juarendra/SlimeVR-BMI160/DOC/slimeVR_2.png

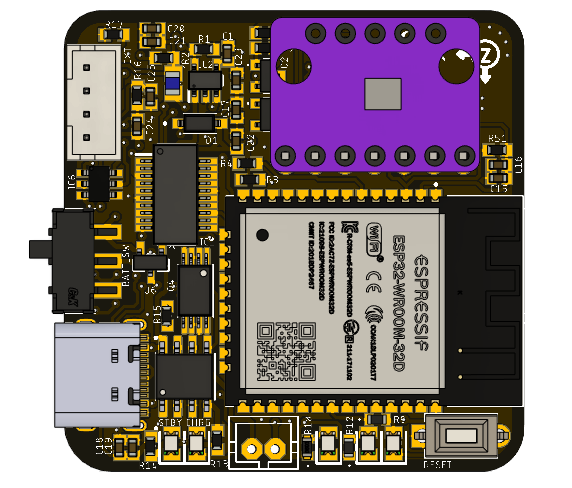
DOC/slimeVR_2.png
