juarendra/SlimeVR-BMI160/DOC/slimeVR_3.png

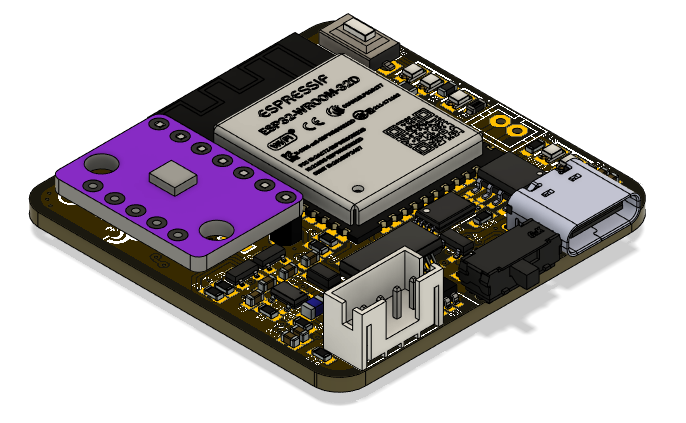
DOC/slimeVR_3.png
