juarendra/SlimeVR-BMI160/DOC/slimeVR_4.png

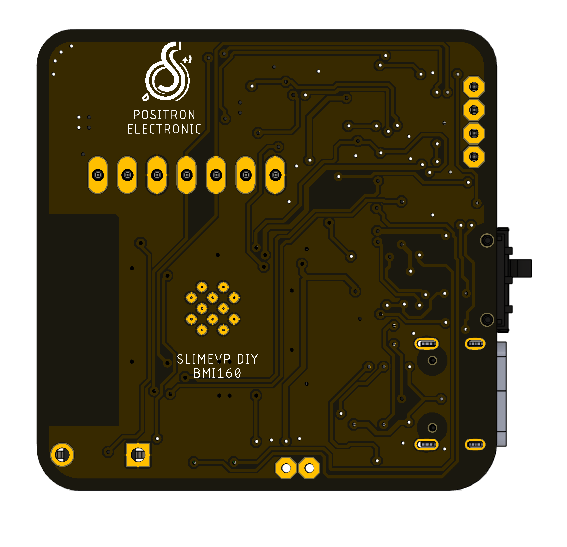
DOC/slimeVR_4.png
