juarendra/SlimeVR-BMI160/DOC/slimeVR_case_2.png

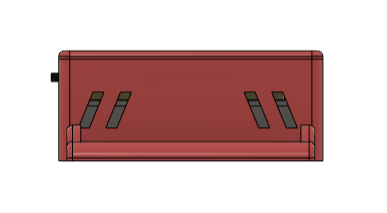
DOC/slimeVR_case_2.png
