juarendra/SlimeVR-BMI160/DOC/slimeVR_case_6.png

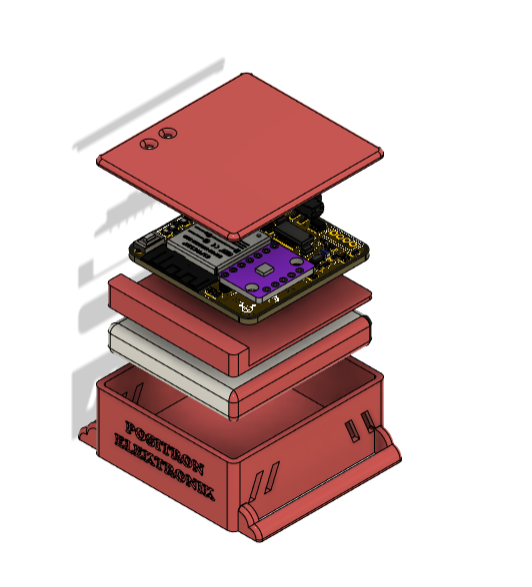
DOC/slimeVR_case_6.png
