juarendra/SlimeVR-BMI160/DOC/slimeVR_real_2.jpeg

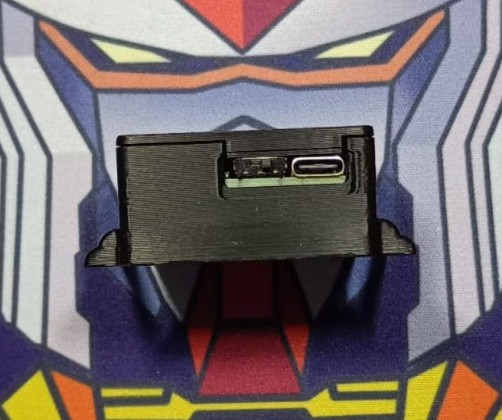
DOC/slimeVR_real_2.jpeg
