juarendra/SlimeVR-BMI160/site/assets/positron.jpg

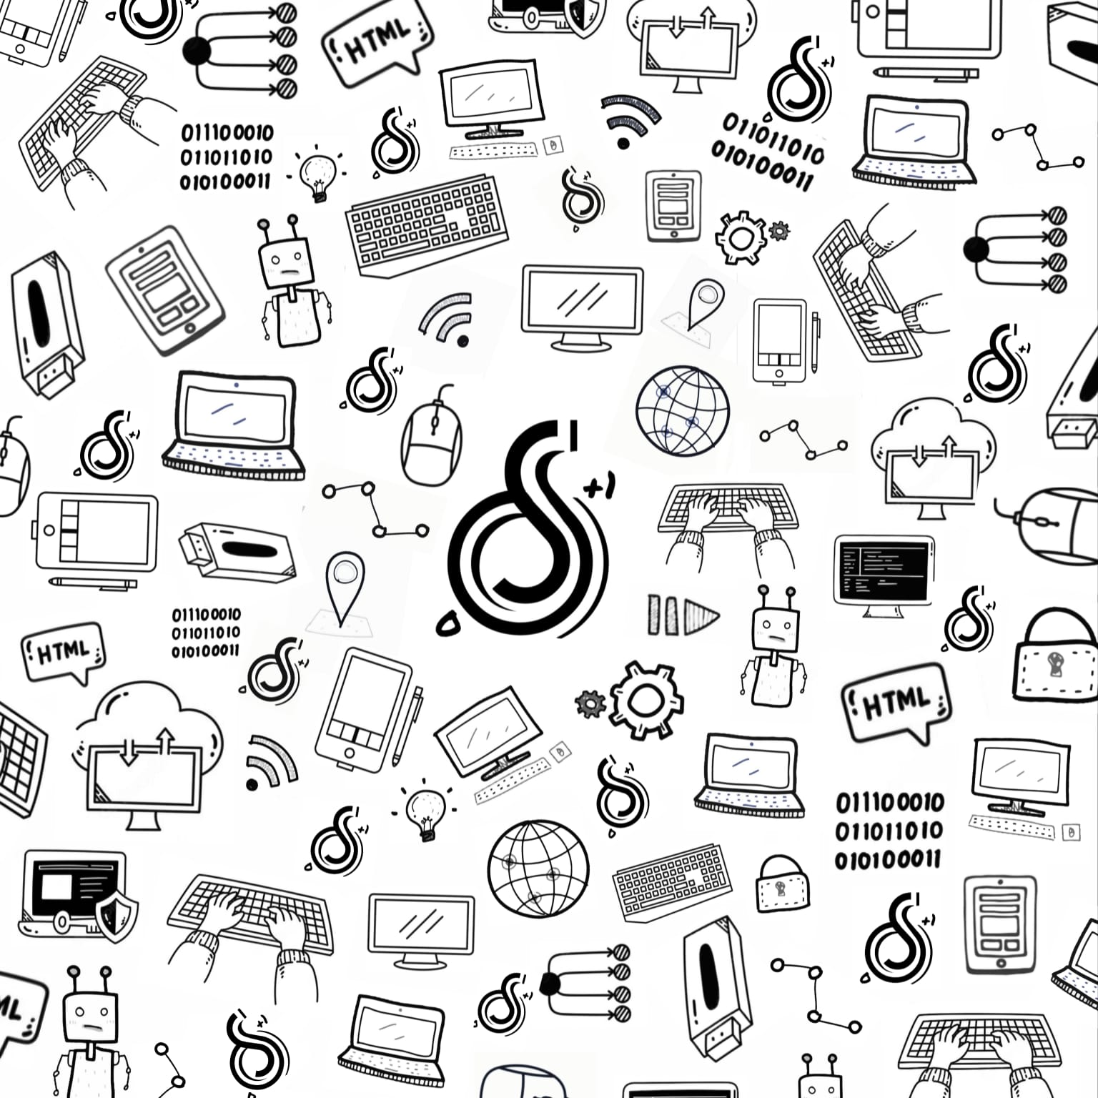
site/assets/positron.jpg
