juarendra/SlimeVR-BMI160/FIRMWARE/SlimeVR-Tracker-ESP/src/batterymonitor.cpp

/*
	SlimeVR Code is placed under the MIT license
	Copyright (c) 2021 Eiren Rain & SlimeVR contributors

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
	THE SOFTWARE IS PROVIDED "AS IS", WITHOUT WARRANTY OF ANY KIND, EXPRESS OR
	IMPLIED, INCLUDING BUT NOT LIMITED TO THE WARRANTIES OF MERCHANTABILITY,
	FITNESS FOR A PARTICULAR PURPOSE AND NONINFRINGEMENT. IN NO EVENT SHALL THE
	AUTHORS OR COPYRIGHT HOLDERS BE LIABLE FOR ANY CLAIM, DAMAGES OR OTHER
	LIABILITY, WHETHER IN AN ACTION OF CONTRACT, TORT OR OTHERWISE, ARISING FROM,
	OUT OF OR IN CONNECTION WITH THE SOFTWARE OR THE USE OR OTHER DEALINGS IN
	THE SOFTWARE.
*/
#include "batterymonitor.h"

#include "GlobalVars.h"

#if ESP8266 \
	&& (BATTERY_MONITOR == BAT_INTERNAL || BATTERY_MONITOR == BAT_INTERNAL_MCP3021)
ADC_MODE(ADC_VCC);
#endif

void BatteryMonitor::Setup() {
#if BATTERY_MONITOR == BAT_MCP3021 || BATTERY_MONITOR == BAT_INTERNAL_MCP3021
	for (uint8_t i = 0x48; i < 0x4F; i++) {
		if (I2CSCAN::hasDevOnBus(i)) {
			address = i;
			break;
		}
	}
	if (address == 0) {
		m_Logger.error("MCP3021 not found on I2C bus");
	}
#endif
}

void BatteryMonitor::Loop() {
#if BATTERY_MONITOR == BAT_EXTERNAL || BATTERY_MONITOR == BAT_INTERNAL \
	|| BATTERY_MONITOR == BAT_MCP3021 || BATTERY_MONITOR == BAT_INTERNAL_MCP3021
	auto now_ms = millis();
	if (now_ms - last_battery_sample >= batterySampleRate) {
		last_battery_sample = now_ms;
		voltage = -1;
#if ESP8266 \
	&& (BATTERY_MONITOR == BAT_INTERNAL || BATTERY_MONITOR == BAT_INTERNAL_MCP3021)
		// Find out what your max measurement is (voltage_3_3).
		// Take the max measurement and check if it was less than 50mV
		// if yes output 5.0V
		// if no output 3.3V - dropvoltage + 0.1V
		auto ESPmV = ESP.getVcc();
		if (ESPmV > voltage_3_3) {
			voltage_3_3 = ESPmV;
		} else {
			// Calculate drop in mV
			ESPmV = voltage_3_3 - ESPmV;
			if (ESPmV < 50) {
				voltage = 5.0F;
			} else {
				voltage = 3.3F - ((float)ESPmV / 1000.0F)
						+ 0.1F;  // we assume 100mV drop on the linear converter
			}
		}
#endif
#if ESP8266 && BATTERY_MONITOR == BAT_EXTERNAL
		voltage = ((float)analogRead(PIN_BATTERY_LEVEL)) * ADCVoltageMax / ADCResolution
				* ADCMultiplier;
#endif
#if defined(ESP32) && BATTERY_MONITOR == BAT_EXTERNAL
		float adcVolts = ((float)analogReadMilliVolts(PIN_BATTERY_LEVEL)) / 1000;
		voltage = adcVolts * ADCMultiplier;
		Serial.printf("[DEBUG] ADCRaw: %.3fV, Multiplier: %.4f, Result: %.3fV\n", adcVolts, ADCMultiplier, voltage);
#endif
#if BATTERY_MONITOR == BAT_MCP3021 || BATTERY_MONITOR == BAT_INTERNAL_MCP3021
		if (address > 0) {
			Wire.beginTransmission(address);
			Wire.requestFrom(address, (uint8_t)2);
			auto MSB = Wire.read();
			auto LSB = Wire.read();
			auto status = Wire.endTransmission();
			if (status == 0) {
				float v = (((uint16_t)(MSB & 0x0F) << 6) | (uint16_t)(LSB >> 2));
				v *= ADCMultiplier;
				voltage = (voltage > 0) ? min(voltage, v) : v;
			}
		}
#endif
		if (voltage > 0)  // valid measurement
		{
			// Estimate battery level, 3.2V is 0%, 4.17V is 100% (1.0)
			if (voltage > 3.975f) {
				level = (voltage - 2.920f) * 0.8f;
			} else if (voltage > 3.678f) {
				level = (voltage - 3.300f) * 1.25f;
			} else if (voltage > 3.489f) {
				level = (voltage - 3.400f) * 1.7f;
			} else if (voltage > 3.360f) {
				level = (voltage - 3.300f) * 0.8f;
			} else {
				level = (voltage - 3.200f) * 0.3f;
			}

			level = (level - 0.05f) / 0.95f;  // Cut off the last 5% (3.36V)

			if (level > 1) {
				level = 1;
			} else if (level < 0) {
				level = 0;
			}
			networkConnection.sendBatteryLevel(voltage, level);
#ifdef BATTERY_LOW_POWER_VOLTAGE
			if (voltage < BATTERY_LOW_POWER_VOLTAGE) {
#if defined(BATTERY_LOW_VOLTAGE_DEEP_SLEEP) && BATTERY_LOW_VOLTAGE_DEEP_SLEEP
				ESP.deepSleep(0);
#else
				statusManager.setStatus(SlimeVR::Status::LOW_BATTERY, true);
#endif
			} else {
				statusManager.setStatus(SlimeVR::Status::LOW_BATTERY, false);
			}
#endif
		}
	}
#endif
}
